rsdlab/SOTA_RakuRakuGuitar/rakuraku_guitar_gui/img1.png

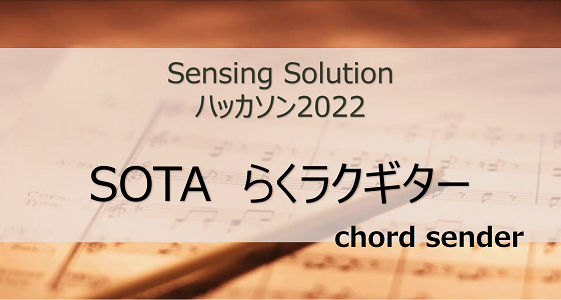
rakuraku_guitar_gui/img1.png
