rsdlab/SOTA_RakuRakuGuitar/rakuraku_guitar_gui/img2.png

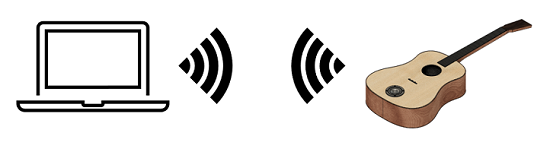
rakuraku_guitar_gui/img2.png
